SonicDyrnv/DP_Group_60/Some_Overviews_In_Image/Screenshot 2025-12-20 130439.png

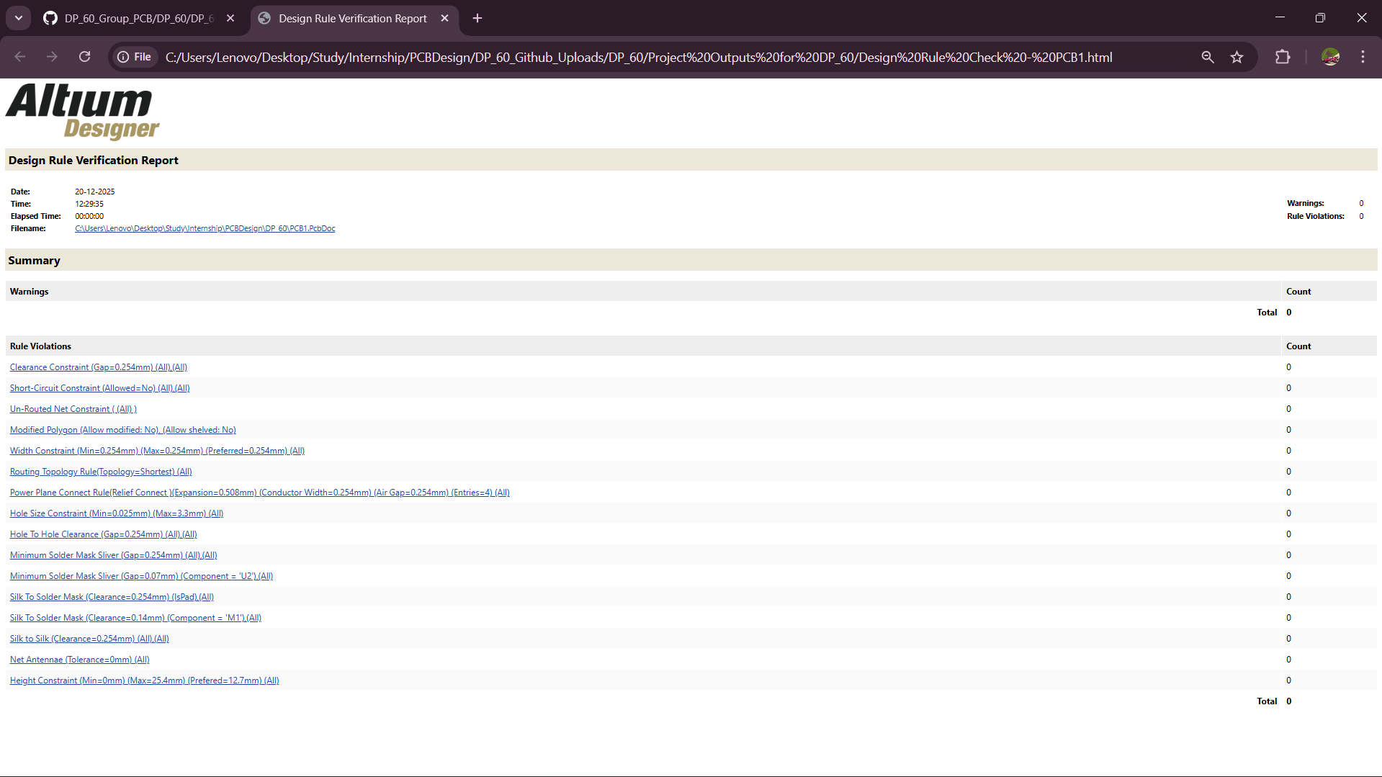
Some_Overviews_In_Image/Screenshot 2025-12-20 130439.png
